dlock8/Selftest_Board/selftest_bd/connector.kicad_sch

## KiCad design selftest_bd/connector.kicad_sch (2025-02-06)

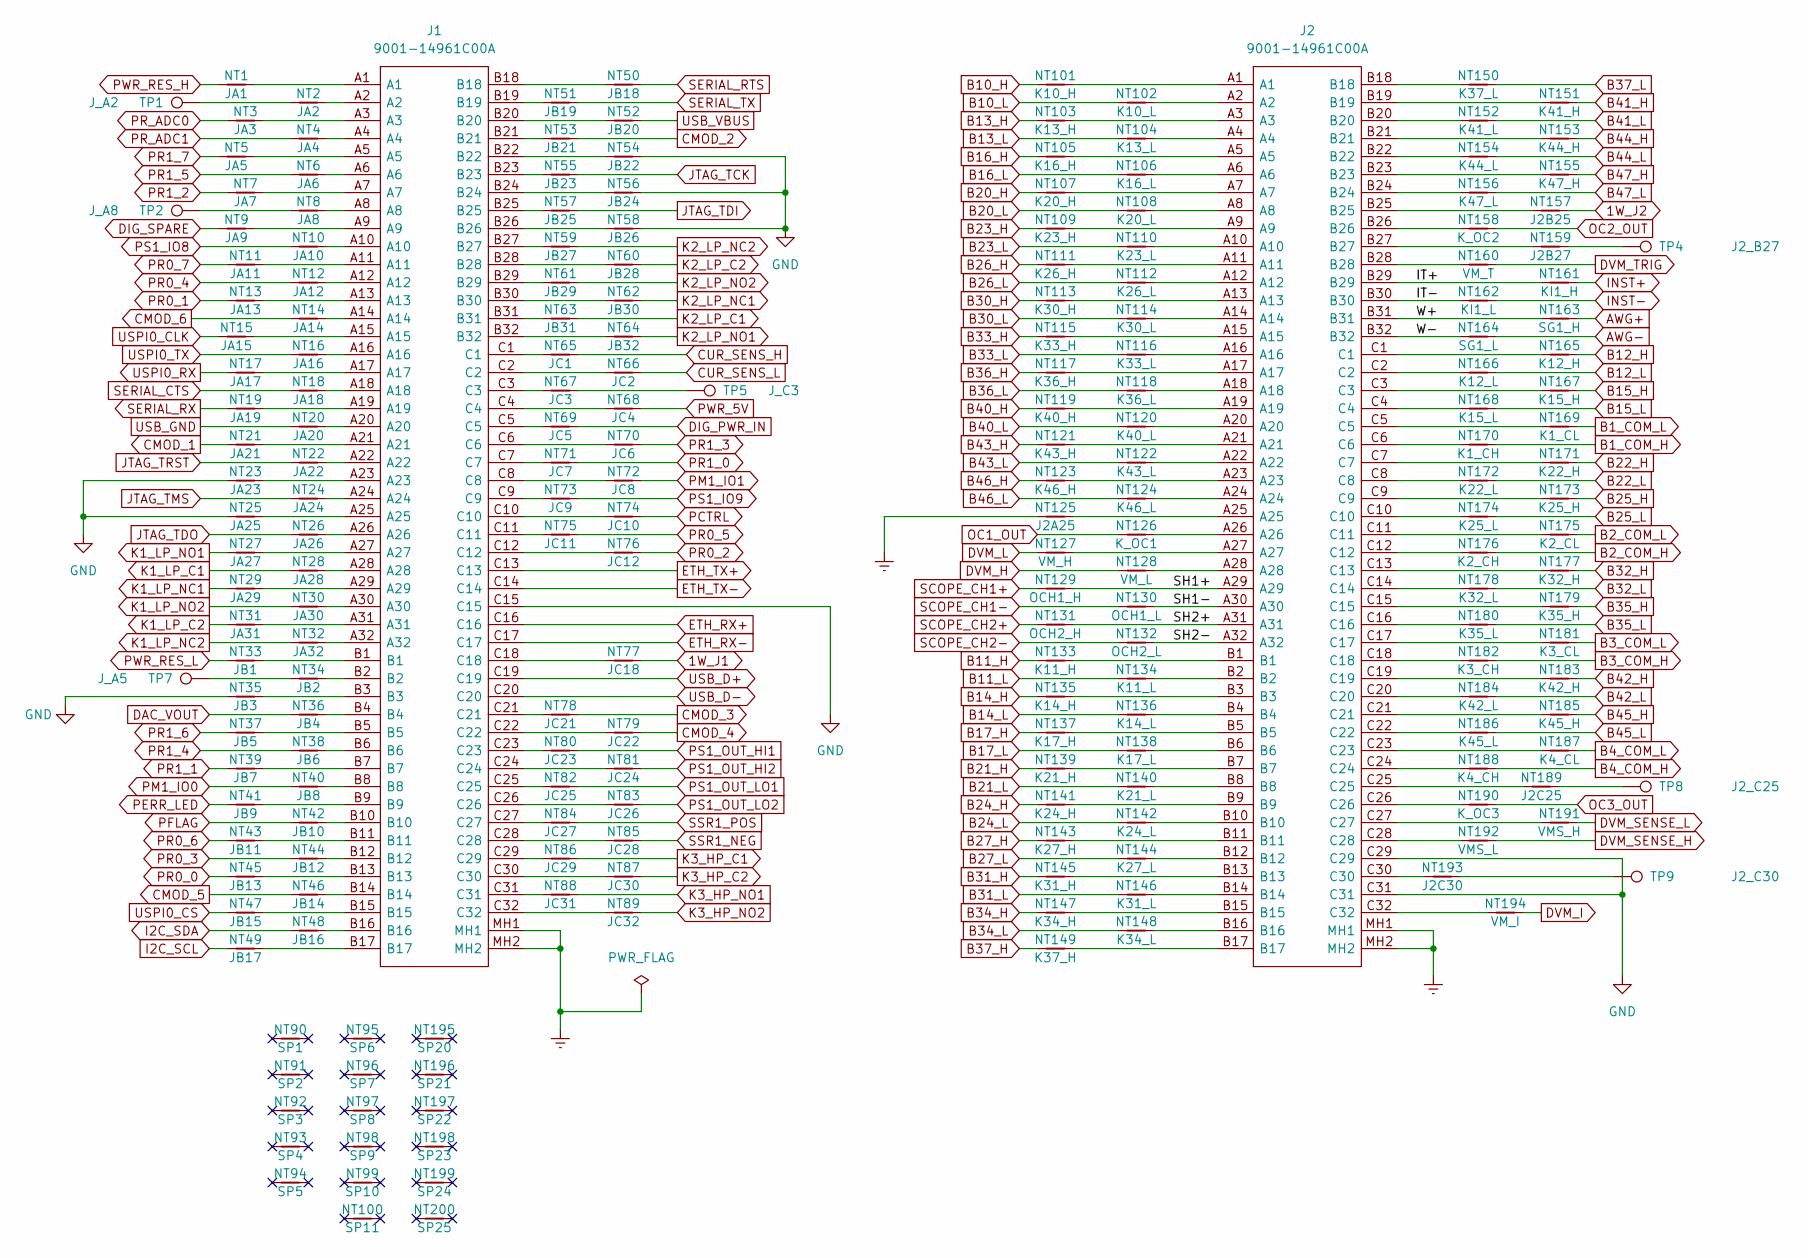
[picture p23: schematic connector.kicad_sch]

Parts:
J1, J2: 9001-14961C00A; 900114961C00A; Manufacturer_Part_Number 9001-14961C00A
NT1: JA1; NetTie-2_Front1.0mm
NT2: JA2; NetTie-2_Front1.0mm
NT3: JA3; NetTie-2_Front1.0mm
NT4: JA4; NetTie-2_Front1.0mm
NT5: JA5; NetTie-2_Front1.0mm
NT6: JA6; NetTie-2_Front1.0mm
NT7: JA7; NetTie-2_Front1.0mm
NT8: JA8; NetTie-2_Front1.0mm
NT9: JA9; NetTie-2_Front1.0mm
NT10: JA10; NetTie-2_Front1.0mm
NT11: JA11; NetTie-2_Front1.0mm
NT12: JA12; NetTie-2_Front1.0mm
NT13: JA13; NetTie-2_Front1.0mm
NT14: JA14; NetTie-2_Front1.0mm
NT15: JA15; NetTie-2_Front1.0mm
NT16: JA16; NetTie-2_Front1.0mm
NT17: JA17; NetTie-2_Front1.0mm
NT18: JA18; NetTie-2_Front1.0mm
NT19: JA19; NetTie-2_Front1.0mm
NT20: JA20; NetTie-2_Front1.0mm
NT21: JA21; NetTie-2_Front1.0mm
NT22: JA22; NetTie-2_Front1.0mm
NT23: JA23; NetTie-2_Front1.0mm
NT24: JA24; NetTie-2_Front1.0mm
NT25: JA25; NetTie-2_Front1.0mm
NT26: JA26; NetTie-2_Front1.0mm
NT27: JA27; NetTie-2_Front1.0mm
NT28: JA28; NetTie-2_Front1.0mm
NT29: JA29; NetTie-2_Front1.0mm
NT30: JA30; NetTie-2_Front1.0mm
NT31: JA31; NetTie-2_Front1.0mm
NT32: JA32; NetTie-2_Front1.0mm
NT33: JB1; NetTie-2_Front1.0mm
NT34: JB2; NetTie-2_Front1.0mm
NT35: JB3; NetTie-2_Front1.0mm
NT36: JB4; NetTie-2_Front1.0mm
NT37: JB5; NetTie-2_Front1.0mm
NT38: JB6; NetTie-2_Front1.0mm
NT39: JB7; NetTie-2_Front1.0mm
NT40: JB8; NetTie-2_Front1.0mm
NT41: JB9; NetTie-2_Front1.0mm
NT42: JB10; NetTie-2_Front1.0mm
NT43: JB11; NetTie-2_Front1.0mm
NT44: JB12; NetTie-2_Front1.0mm
NT45: JB13; NetTie-2_Front1.0mm
NT46: JB14; NetTie-2_Front1.0mm
NT47: JB15; NetTie-2_Front1.0mm
NT48: JB16; NetTie-2_Front1.0mm
NT49: JB17; NetTie-2_Front1.0mm
NT50: JB18; NetTie-2_Front1.0mm
NT51: JB19; NetTie-2_Front1.0mm
NT52: JB20; NetTie-2_Front1.0mm
NT53: JB21; NetTie-2_Front1.0mm
NT54: JB22; NetTie-2_Front1.0mm
NT55: JB23; NetTie-2_Front1.0mm
NT56: JB24; NetTie-2_Front1.0mm
NT57: JB25; NetTie-2_Front1.0mm
NT58: JB26; NetTie-2_Front1.0mm
NT59: JB27; NetTie-2_Front1.0mm
NT60: JB28; NetTie-2_Front1.0mm
NT61: JB29; NetTie-2_Front1.0mm
NT62: JB30; NetTie-2_Front1.0mm
NT63: JB31; NetTie-2_Front1.0mm
NT64: JB32; NetTie-2_Front1.0mm
NT65: JC1; NetTie-2_Front1.0mm
NT66: JC2; NetTie-2_Front1.0mm
NT67: JC3; NetTie-2_Front1.0mm
NT68: JC4; NetTie-2_Front1.0mm
NT69: JC5; NetTie-2_Front1.0mm
NT70: JC6; NetTie-2_Front1.0mm
NT71: JC7; NetTie-2_Front1.0mm
NT72: JC8; NetTie-2_Front1.0mm
NT73: JC9; NetTie-2_Front1.0mm
NT74: JC10; NetTie-2_Front1.0mm
NT75: JC11; NetTie-2_Front1.0mm
NT76: JC12; NetTie-2_Front1.0mm
NT77: JC18; NetTie-2_Front1.0mm
NT78: JC21; NetTie-2_Front1.0mm
NT79: JC22; NetTie-2_Front1.0mm
NT80: JC23; NetTie-2_Front1.0mm
NT81: JC24; NetTie-2_Front1.0mm
NT82: JC25; NetTie-2_Front1.0mm
NT83: JC26; NetTie-2_Front1.0mm
NT84: JC27; NetTie-2_Front1.0mm
NT85: JC28; NetTie-2_Front1.0mm
NT86: JC29; NetTie-2_Front1.0mm
NT87: JC30; NetTie-2_Front1.0mm
NT88: JC31; NetTie-2_Front1.0mm
NT89: JC32; NetTie-2_Front1.0mm
NT90: SP1; NetTie-2_Front1.0mm
NT91: SP2; NetTie-2_Front1.0mm
NT92: SP3; NetTie-2_Front1.0mm
NT93: SP4; NetTie-2_Front1.0mm
NT94: SP5; NetTie-2_Front1.0mm
NT95: SP6; NetTie-2_Front1.0mm
NT96: SP7; NetTie-2_Front1.0mm
NT97: SP8; NetTie-2_Front1.0mm
NT98: SP9; NetTie-2_Front1.0mm
NT99: SP10; NetTie-2_Front1.0mm
NT100: SP11; NetTie-2_Front1.0mm
NT101: K10_H; NetTie-2_Front1.0mm
NT102: K10_L; NetTie-2_Front1.0mm
NT103: K13_H; NetTie-2_Front1.0mm
NT104: K13_L; NetTie-2_Front1.0mm
NT105: K16_H; NetTie-2_Front1.0mm
NT106: K16_L; NetTie-2_Front1.0mm
NT107: K20_H; NetTie-2_Front1.0mm
NT108: K20_L; NetTie-2_Front1.0mm
NT109: K23_H; NetTie-2_Front1.0mm
NT110: K23_L; NetTie-2_Front1.0mm
NT111: K26_H; NetTie-2_Front1.0mm
NT112: K26_L; NetTie-2_Front1.0mm
NT113: K30_H; NetTie-2_Front1.0mm
NT114: K30_L; NetTie-2_Front1.0mm
NT115: K33_H; NetTie-2_Front1.0mm
NT116: K33_L; NetTie-2_Front1.0mm
NT117: K36_H; NetTie-2_Front1.0mm
NT118: K36_L; NetTie-2_Front1.0mm
NT119: K40_H; NetTie-2_Front1.0mm
NT120: K40_L; NetTie-2_Front1.0mm
NT121: K43_H; NetTie-2_Front1.0mm
NT122: K43_L; NetTie-2_Front1.0mm
NT123: K46_H; NetTie-2_Front1.0mm
NT124: K46_L; NetTie-2_Front1.0mm
NT125: J2A25; NetTie-2_Front1.0mm
NT126: K_OC1; NetTie-2_Front1.0mm
NT127: VM_H; NetTie-2_Front1.0mm
NT128: VM_L; NetTie-2_Front1.0mm
NT129: OCH1_H; NetTie-2_Front1.0mm
NT130: OCH1_L; NetTie-2_Front1.0mm
NT131: OCH2_H; NetTie-2_Front1.0mm
NT132: OCH2_L; NetTie-2_Front1.0mm
NT133: K11_H; NetTie-2_Front1.0mm
NT134: K11_L; NetTie-2_Front1.0mm
NT135: K14_H; NetTie-2_Front1.0mm
NT136: K14_L; NetTie-2_Front1.0mm
NT137: K17_H; NetTie-2_Front1.0mm
NT138: K17_L; NetTie-2_Front1.0mm
NT139: K21_H; NetTie-2_Front1.0mm
NT140: K21_L; NetTie-2_Front1.0mm
NT141: K24_H; NetTie-2_Front1.0mm
NT142: K24_L; NetTie-2_Front1.0mm
NT143: K27_H; NetTie-2_Front1.0mm
NT144: K27_L; NetTie-2_Front1.0mm
NT145: K31_H; NetTie-2_Front1.0mm
NT146: K31_L; NetTie-2_Front1.0mm
NT147: K34_H; NetTie-2_Front1.0mm
NT148: K34_L; NetTie-2_Front1.0mm
NT149: K37_H; NetTie-2_Front1.0mm
NT150: K37_L; NetTie-2_Front1.0mm
NT151: K41_H; NetTie-2_Front1.0mm
NT152: K41_L; NetTie-2_Front1.0mm
NT153: K44_H; NetTie-2_Front1.0mm
NT154: K44_L; NetTie-2_Front1.0mm
NT155: K47_H; NetTie-2_Front1.0mm
NT156: K47_L; NetTie-2_Front1.0mm
NT157: J2B25; NetTie-2_Front1.0mm
NT158: K_OC2; NetTie-2_Front1.0mm
NT159: J2B27; NetTie-2_Front1.0mm
NT160: VM_T; NetTie-2_Front1.0mm
NT161: KI1_H; NetTie-2_Front1.0mm
NT162: KI1_L; NetTie-2_Front1.0mm
NT163: SG1_H; NetTie-2_Front1.0mm
NT164: SG1_L; NetTie-2_Front1.0mm
NT165: K12_H; NetTie-2_Front1.0mm
NT166: K12_L; NetTie-2_Front1.0mm
NT167: K15_H; NetTie-2_Front1.0mm
NT168: K15_L; NetTie-2_Front1.0mm
NT169: K1_CL; NetTie-2_Front1.0mm
NT170: K1_CH; NetTie-2_Front1.0mm
NT171: K22_H; NetTie-2_Front1.0mm
NT172: K22_L; NetTie-2_Front1.0mm
NT173: K25_H; NetTie-2_Front1.0mm
NT174: K25_L; NetTie-2_Front1.0mm
NT175: K2_CL; NetTie-2_Front1.0mm
NT176: K2_CH; NetTie-2_Front1.0mm
NT177: K32_H; NetTie-2_Front1.0mm
NT178: K32_L; NetTie-2_Front1.0mm
NT179: K35_H; NetTie-2_Front1.0mm
NT180: K35_L; NetTie-2_Front1.0mm
NT181: K3_CL; NetTie-2_Front1.0mm
NT182: K3_CH; NetTie-2_Front1.0mm
NT183: K42_H; NetTie-2_Front1.0mm
NT184: K42_L; NetTie-2_Front1.0mm
NT185: K45_H; NetTie-2_Front1.0mm
NT186: K45_L; NetTie-2_Front1.0mm
NT187: K4_CL; NetTie-2_Front1.0mm
NT188: K4_CH; NetTie-2_Front1.0mm
NT189: J2C25; NetTie-2_Front1.0mm
NT190: K_OC3; NetTie-2_Front1.0mm
NT191: VMS_H; NetTie-2_Front1.0mm
NT192: VMS_L; NetTie-2_Front1.0mm
NT193: J2C30; NetTie-2_Front1.0mm
NT194: VM_I; NetTie-2_Front1.0mm
NT195: SP20; NetTie-2_Front1.0mm
NT196: SP21; NetTie-2_Front1.0mm
NT197: SP22; NetTie-2_Front1.0mm
NT198: SP23; NetTie-2_Front1.0mm
NT199: SP24; NetTie-2_Front1.0mm
NT200: SP25; NetTie-2_Front1.0mm
TP1: J_A2; TestPoint_THTPad_D1.5mm_Drill0.7mm
TP2: J_A8; TestPoint_THTPad_D1.5mm_Drill0.7mm
TP4: J2_B27; TestPoint_THTPad_D1.5mm_Drill0.7mm
TP5: J_C3; TestPoint_THTPad_D1.5mm_Drill0.7mm
TP7: J_A5; TestPoint_THTPad_D1.5mm_Drill0.7mm
TP8: J2_C25; TestPoint_THTPad_D1.5mm_Drill0.7mm
TP9: J2_C30; TestPoint_THTPad_D1.5mm_Drill0.7mm

Connections:
1W_J1: NT77.1
1W_J2: NT157.2
AWG+: NT163.2
AWG-: NT164.2
B1_COM_H: NT170.1
B1_COM_L: NT169.1
B2_COM_H: NT176.1
B2_COM_L: NT175.1
B3_COM_H: NT182.2
B3_COM_L: NT181.2
B4_COM_H: NT188.1
B4_COM_L: NT187.1
B10_H: NT101.2
B10_L: NT102.2
B11_H: NT133.2
B11_L: NT134.2
B12_H: NT165.2
B12_L: NT166.2
B13_H: NT103.2
B13_L: NT104.2
B14_H: NT135.2
B14_L: NT136.2
B15_H: NT167.2
B15_L: NT168.2
B16_H: NT105.2
B16_L: NT106.2
B17_H: NT137.2
B17_L: NT138.2
B20_H: NT107.2
B20_L: NT108.2
B21_H: NT139.2
B21_L: NT140.2
B22_H: NT171.2
B22_L: NT172.2
B23_H: NT109.2
B23_L: NT110.2
B24_H: NT141.2
B24_L: NT142.2
B25_H: NT173.2
B25_L: NT174.2
B26_H: NT111.2
B26_L: NT112.2
B27_H: NT143.2
B27_L: NT144.2
B30_H: NT113.2
B30_L: NT114.2
B31_H: NT145.2
B31_L: NT146.2
B32_H: NT177.2
B32_L: NT178.2
B33_H: NT115.2
B33_L: NT116.2
B34_H: NT147.2
B34_L: NT148.2
B35_H: NT179.2
B35_L: NT180.2
B36_H: NT117.2
B36_L: NT118.2
B37_H: NT149.2
B37_L: NT150.2
B40_H: NT119.2
B40_L: NT120.2
B41_H: NT151.2
B41_L: NT152.2
B42_H: NT183.1
B42_L: NT184.2
B43_H: NT121.2
B43_L: NT122.2
B44_H: NT153.2
B44_L: NT154.2
B45_H: NT185.2
B45_L: NT186.2
B46_H: NT123.2
B46_L: NT124.2
B47_H: NT155.2
B47_L: NT156.2
CMOD_1: NT21.1
CMOD_2: NT53.1
CMOD_3: NT78.1
CMOD_4: NT79.1
CMOD_5: NT46.1
CMOD_6: NT14.1
CUR_SENS_H: NT65.1
CUR_SENS_L: NT66.1
DAC_VOUT: NT36.1
DIG_PWR_IN: NT69.1
DIG_SPARE: NT9.1
DVM_H: NT128.2
DVM_I: NT194.2
DVM_L: NT127.2
DVM_SENSE_H: NT192.2
DVM_SENSE_L: NT191.2
DVM_TRIG: NT160.2
ETH_RX+: J1.C16
ETH_RX-: J1.C17
ETH_TX+: J1.C13
ETH_TX-: J1.C14
Earth: J1.MH1, J1.MH2, J2.MH1, J2.MH2, NT125.2
GND: J1.C15, J2.C29, J2.C31, NT23.1, NT25.1, NT35.1, NT54.1, NT56.1, NT58.1
I2C_SCL: NT49.1
I2C_SDA: NT48.1
INST+: NT161.1
INST-: NT162.1
IT+: J2.B29, NT161.2
IT-: J2.B30, NT162.2
JTAG_TCK: NT55.1
JTAG_TDI: NT57.1
JTAG_TDO: NT26.1
JTAG_TMS: NT24.1
JTAG_TRST: NT22.1
K1_LP_C1: NT28.1
K1_LP_C2: NT31.1
K1_LP_NC1: NT29.1
K1_LP_NC2: NT32.1
K1_LP_NO1: NT27.1
K1_LP_NO2: NT30.1
K2_LP_C1: NT63.1
K2_LP_C2: NT60.1
K2_LP_NC1: NT62.1
K2_LP_NC2: NT59.1
K2_LP_NO1: NT64.1
K2_LP_NO2: NT61.1
K3_HP_C1: NT86.1
K3_HP_C2: NT87.1
K3_HP_NO1: NT88.1
K3_HP_NO2: NT89.1
unnamed: J1.A1, NT1.2
unnamed: J1.A2, NT2.2
unnamed: J1.A3, NT3.2
unnamed: J1.A4, NT4.2
unnamed: J1.A5, NT5.2
unnamed: J1.A6, NT6.2
unnamed: J1.A7, NT7.2
unnamed: J1.A8, NT8.2
unnamed: J1.A9, NT9.2
unnamed: J1.A10, NT10.2
unnamed: J1.A11, NT11.2
unnamed: J1.A12, NT12.2
unnamed: J1.A13, NT13.2
unnamed: J1.A14, NT14.2
unnamed: J1.A15, NT15.2
unnamed: J1.A16, NT16.2
unnamed: J1.A17, NT17.2
unnamed: J1.A18, NT18.2
unnamed: J1.A19, NT19.2
unnamed: J1.A20, NT20.2
unnamed: J1.A21, NT21.2
unnamed: J1.A22, NT22.2
unnamed: J1.A23, NT23.2
unnamed: J1.A24, NT24.2
unnamed: J1.A25, NT25.2
unnamed: J1.A26, NT26.2
unnamed: J1.A27, NT27.2
unnamed: J1.A28, NT28.2
unnamed: J1.A29, NT29.2
unnamed: J1.A30, NT30.2
unnamed: J1.A31, NT31.2
unnamed: J1.A32, NT32.2
unnamed: J1.B1, NT33.2
unnamed: J1.B2, NT34.2
unnamed: J1.B3, NT35.2
unnamed: J1.B4, NT36.2
unnamed: J1.B5, NT37.2
unnamed: J1.B6, NT38.2
unnamed: J1.B7, NT39.2
unnamed: J1.B8, NT40.2
unnamed: J1.B9, NT41.2
unnamed: J1.B10, NT42.2
unnamed: J1.B11, NT43.2
unnamed: J1.B12, NT44.2
unnamed: J1.B13, NT45.2
unnamed: J1.B14, NT46.2
unnamed: J1.B15, NT47.2
unnamed: J1.B16, NT48.2
unnamed: J1.B17, NT49.2
unnamed: J1.B18, NT50.2
unnamed: J1.B19, NT51.2
unnamed: J1.B20, NT52.2
unnamed: J1.B21, NT53.2
unnamed: J1.B22, NT54.2
unnamed: J1.B23, NT55.2
unnamed: J1.B24, NT56.2
unnamed: J1.B25, NT57.2
unnamed: J1.B26, NT58.2
unnamed: J1.B27, NT59.2
unnamed: J1.B28, NT60.2
unnamed: J1.B29, NT61.2
unnamed: J1.B30, NT62.2
unnamed: J1.B31, NT63.2
unnamed: J1.B32, NT64.2
unnamed: J1.C1, NT65.2
unnamed: J1.C2, NT66.2
unnamed: J1.C3, NT67.2
unnamed: J1.C4, NT68.2
unnamed: J1.C5, NT69.2
unnamed: J1.C6, NT70.2
unnamed: J1.C7, NT71.2
unnamed: J1.C8, NT72.2
unnamed: J1.C9, NT73.2
unnamed: J1.C10, NT74.2
unnamed: J1.C11, NT75.2
unnamed: J1.C12, NT76.2
unnamed: J1.C18, NT77.2
unnamed: J1.C21, NT78.2
unnamed: J1.C22, NT79.2
unnamed: J1.C23, NT80.2
unnamed: J1.C24, NT81.2
unnamed: J1.C25, NT82.2
unnamed: J1.C26, NT83.2
unnamed: J1.C27, NT84.2
unnamed: J1.C28, NT85.2
unnamed: J1.C29, NT86.2
unnamed: J1.C30, NT87.2
unnamed: J1.C31, NT88.2
unnamed: J1.C32, NT89.2
unnamed: J2.A1, NT101.1
unnamed: J2.A2, NT102.1
unnamed: J2.A3, NT103.1
unnamed: J2.A4, NT104.1
unnamed: J2.A5, NT105.1
unnamed: J2.A6, NT106.1
unnamed: J2.A7, NT107.1
unnamed: J2.A8, NT108.1
unnamed: J2.A9, NT109.1
unnamed: J2.A10, NT110.1
unnamed: J2.A11, NT111.1
unnamed: J2.A12, NT112.1
unnamed: J2.A13, NT113.1
unnamed: J2.A14, NT114.1
unnamed: J2.A15, NT115.1
unnamed: J2.A16, NT116.1
unnamed: J2.A17, NT117.1
unnamed: J2.A18, NT118.1
unnamed: J2.A19, NT119.1
unnamed: J2.A20, NT120.1
unnamed: J2.A21, NT121.1
unnamed: J2.A22, NT122.1
unnamed: J2.A23, NT123.1
unnamed: J2.A24, NT124.1
unnamed: J2.A25, NT125.1
unnamed: J2.A26, NT126.2
unnamed: J2.A27, NT127.1
unnamed: J2.A28, NT128.1
unnamed: J2.B1, NT133.1
unnamed: J2.B2, NT134.1
unnamed: J2.B3, NT135.1
unnamed: J2.B4, NT136.1
unnamed: J2.B5, NT137.1
unnamed: J2.B6, NT138.1
unnamed: J2.B7, NT139.1
unnamed: J2.B8, NT140.1
unnamed: J2.B9, NT141.1
unnamed: J2.B10, NT142.1
unnamed: J2.B11, NT143.1
unnamed: J2.B12, NT144.1
unnamed: J2.B13, NT145.1
unnamed: J2.B14, NT146.1
unnamed: J2.B15, NT147.1
unnamed: J2.B16, NT148.1
unnamed: J2.B17, NT149.1
unnamed: J2.B18, NT150.1
unnamed: J2.B19, NT151.1
unnamed: J2.B20, NT152.1
unnamed: J2.B21, NT153.1
unnamed: J2.B22, NT154.1
unnamed: J2.B23, NT155.1
unnamed: J2.B24, NT156.1
unnamed: J2.B25, NT157.1
unnamed: J2.B26, NT158.2
unnamed: J2.B27, NT159.1
unnamed: J2.B28, NT160.1
unnamed: J2.C1, NT165.1
unnamed: J2.C2, NT166.1
unnamed: J2.C3, NT167.1
unnamed: J2.C4, NT168.1
unnamed: J2.C5, NT169.2
unnamed: J2.C6, NT170.2
unnamed: J2.C7, NT171.1
unnamed: J2.C8, NT172.1
unnamed: J2.C9, NT173.1
unnamed: J2.C10, NT174.1
unnamed: J2.C11, NT175.2
unnamed: J2.C12, NT176.2
unnamed: J2.C13, NT177.1
unnamed: J2.C14, NT178.1
unnamed: J2.C15, NT179.1
unnamed: J2.C16, NT180.1
unnamed: J2.C17, NT181.1
unnamed: J2.C18, NT182.1
unnamed: J2.C19, NT183.2
unnamed: J2.C20, NT184.1
unnamed: J2.C21, NT185.1
unnamed: J2.C22, NT186.1
unnamed: J2.C23, NT187.2
unnamed: J2.C24, NT188.2
unnamed: J2.C25, NT189.2
unnamed: J2.C26, NT190.2
unnamed: J2.C27, NT191.1
unnamed: J2.C28, NT192.1
unnamed: J2.C30, NT193.1
unnamed: J2.C32, NT194.1
unnamed: NT2.1, TP1.1
unnamed: NT8.1, TP2.1
unnamed: NT34.1, TP7.1
unnamed: NT67.1, TP5.1
unnamed: NT159.2, TP4.1
unnamed: NT189.1, TP8.1
unnamed: NT193.2, TP9.1
OC1_OUT: NT126.1
OC2_OUT: NT158.1
OC3_OUT: NT190.1
PCTRL: NT74.1
PERR_LED: NT41.1
PFLAG: NT42.1
PM1_IO0: NT40.1
PM1_IO1: NT72.1
PR0_0: NT45.1
PR0_1: NT13.1
PR0_2: NT76.1
PR0_3: NT44.1
PR0_4: NT12.1
PR0_5: NT75.1
PR0_6: NT43.1
PR0_7: NT11.1
PR1_0: NT71.1
PR1_1: NT39.1
PR1_2: NT7.1
PR1_3: NT70.1
PR1_4: NT38.1
PR1_5: NT6.1
PR1_6: NT37.1
PR1_7: NT5.1
PR_ADC0: NT3.1
PR_ADC1: NT4.1
PS1_IO8: NT10.1
PS1_IO9: NT73.1
PS1_OUT_HI1: NT80.1
PS1_OUT_HI2: NT81.1
PS1_OUT_LO1: NT82.1
PS1_OUT_LO2: NT83.1
PWR_5V: NT68.1
PWR_RES_H: NT1.1
PWR_RES_L: NT33.1
SCOPE_CH1+: NT129.2
SCOPE_CH1-: NT130.2
SCOPE_CH2+: NT131.1
SCOPE_CH2-: NT132.1
SERIAL_CTS: NT18.1
SERIAL_RTS: NT50.1
SERIAL_RX: NT19.1
SERIAL_TX: NT51.1
SH1+: J2.A29, NT129.1
SH1-: J2.A30, NT130.1
SH2+: J2.A31, NT131.2
SH2-: J2.A32, NT132.2
SSR1_NEG: NT85.1
SSR1_POS: NT84.1
USB_D+: J1.C19
USB_D-: J1.C20
USB_GND: NT20.1
USB_VBUS: NT52.1
USPI0_CLK: NT15.1
USPI0_CS: NT47.1
USPI0_RX: NT17.1
USPI0_TX: NT16.1
W+: J2.B31, NT163.1
W-: J2.B32, NT164.1
