dlock8/Selftest_Board/selftest_bd/controller.kicad_sch

## KiCad design selftest_bd/controller.kicad_sch (2024-11-22)

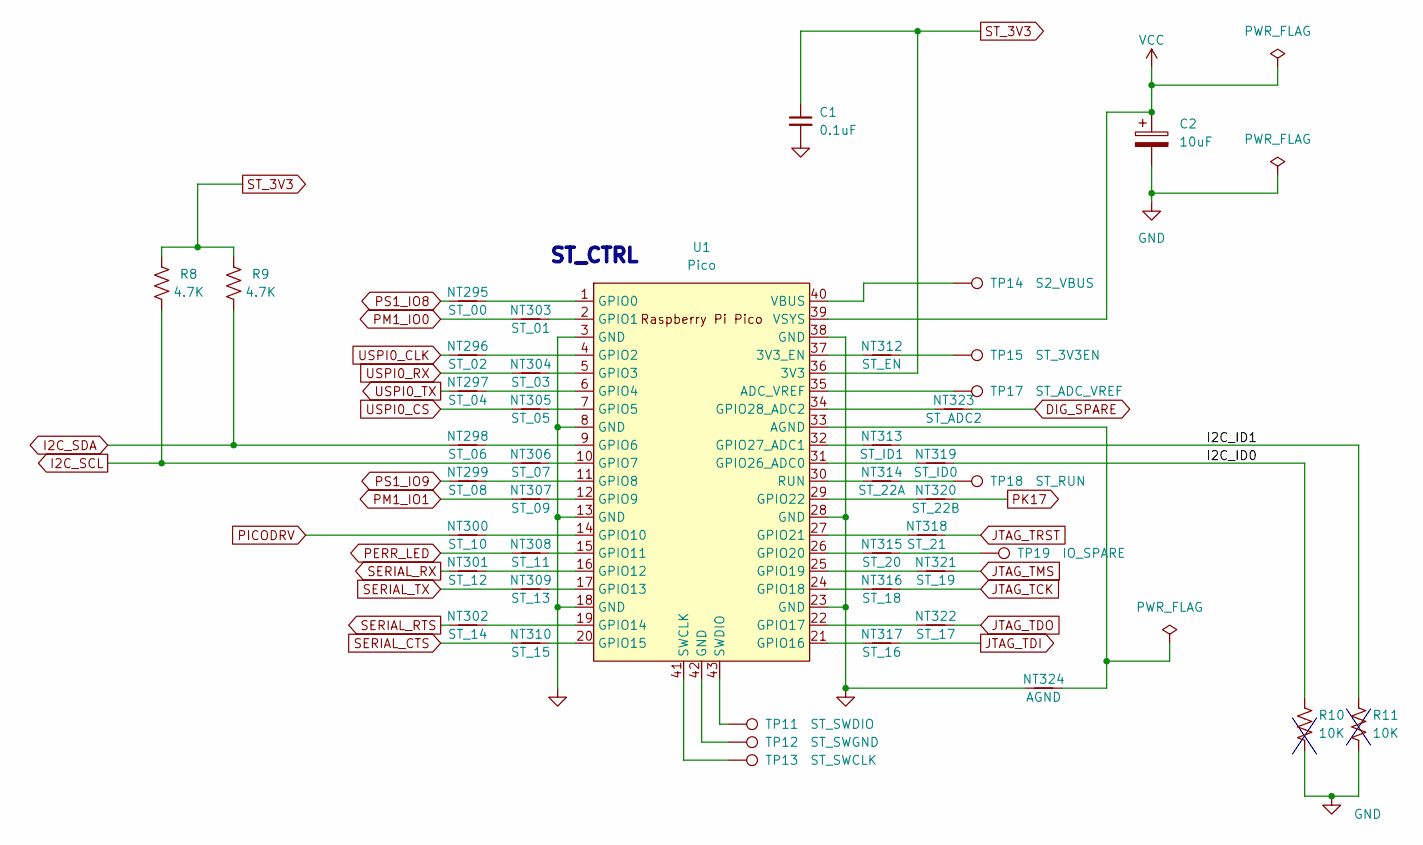
[picture p24: schematic controller.kicad_sch]

Parts:
C1: 0.1uF; C_Disc_D6.0mm_W2.5mm_P5.00mm
C2: 10uF; CP_Radial_Tantal_D4.5mm_P2.50mm
NT295: ST_00; NetTie-2_Front1.0mm
NT296: ST_02; NetTie-2_Front1.0mm
NT297: ST_04; NetTie-2_Front1.0mm
NT298: ST_06; NetTie-2_Front1.0mm
NT299: ST_08; NetTie-2_Front1.0mm
NT300: ST_10; NetTie-2_Front1.0mm
NT301: ST_12; NetTie-2_Front1.0mm
NT302: ST_14; NetTie-2_Front1.0mm
NT303: ST_01; NetTie-2_Front1.0mm
NT304: ST_03; NetTie-2_Front1.0mm
NT305: ST_05; NetTie-2_Front1.0mm
NT306: ST_07; NetTie-2_Front1.0mm
NT307: ST_09; NetTie-2_Front1.0mm
NT308: ST_11; NetTie-2_Front1.0mm
NT309: ST_13; NetTie-2_Front1.0mm
NT310: ST_15; NetTie-2_Front1.0mm
NT312: ST_EN; NetTie-2_Front1.0mm
NT313: ST_ID1; NetTie-2_Front1.0mm
NT314: ST_22A; NetTie-2_Front1.0mm
NT315: ST_20; NetTie-2_Front1.0mm
NT316: ST_18; NetTie-2_Front1.0mm
NT317: ST_16; NetTie-2_Front1.0mm
NT318: ST_21; NetTie-2_Front1.0mm
NT319: ST_ID0; NetTie-2_Front1.0mm
NT320: ST_22B; NetTie-2_Front1.0mm
NT321: ST_19; NetTie-2_Front1.0mm
NT322: ST_17; NetTie-2_Front1.0mm
NT323: ST_ADC2; NetTie-2_Front1.0mm
NT324: AGND; NetTie-2_Front1.0mm
R8, R9: 4.7K; R_Axial_DIN0207_L6.3mm_D2.5mm_P10.16mm_Horizontal
R10, R11: 10K; R_Axial_DIN0207_L6.3mm_D2.5mm_P10.16mm_Horizontal
TP11: ST_SWDIO; TestPoint_THTPad_D1.5mm_Drill0.7mm
TP12: ST_SWGND; TestPoint_THTPad_D1.5mm_Drill0.7mm
TP13: ST_SWCLK; TestPoint_THTPad_D1.5mm_Drill0.7mm
TP14: S2_VBUS; TestPoint_THTPad_D1.5mm_Drill0.7mm
TP15: ST_3V3EN; TestPoint_THTPad_D1.5mm_Drill0.7mm
TP17: ST_ADC_VREF; TestPoint_THTPad_D1.5mm_Drill0.7mm
TP18: ST_RUN; TestPoint_THTPad_D1.5mm_Drill0.7mm
TP19: IO_SPARE; TestPoint_THTPad_D1.5mm_Drill0.7mm
U1: Pico; RPi_Pico_SMD_TH

Connections:
DIG_SPARE: NT323.1
GND: C1.2, C2.2, NT324.2, R10.1, R11.1, U1.3 (GND), U1.8 (GND), U1.13 (GND), U1.18 (GND), U1.23 (GND), U1.28 (GND), U1.38 (GND)
I2C_ID0: NT319.1, R10.2
I2C_ID1: NT313.1, R11.2
I2C_SCL: NT306.1, R8.1
I2C_SDA: NT298.1, R9.1
JTAG_TCK: NT316.1
JTAG_TDI: NT317.1
JTAG_TDO: NT322.1
JTAG_TMS: NT321.1
JTAG_TRST: NT318.1
unnamed: NT295.2, U1.1 (GPIO0)
unnamed: NT296.2, U1.4 (GPIO2)
unnamed: NT297.2, U1.6 (GPIO4)
unnamed: NT298.2, U1.9 (GPIO6)
unnamed: NT299.2, U1.11 (GPIO8)
unnamed: NT300.2, U1.14 (GPIO10)
unnamed: NT301.2, U1.16 (GPIO12)
unnamed: NT302.2, U1.19 (GPIO14)
unnamed: NT303.2, U1.2 (GPIO1)
unnamed: NT304.2, U1.5 (GPIO3)
unnamed: NT305.2, U1.7 (GPIO5)
unnamed: NT306.2, U1.10 (GPIO7)
unnamed: NT307.2, U1.12 (GPIO9)
unnamed: NT308.2, U1.15 (GPIO11)
unnamed: NT309.2, U1.17 (GPIO13)
unnamed: NT310.2, U1.20 (GPIO15)
unnamed: NT312.1, U1.37 (3V3_EN)
unnamed: NT312.2, TP15.1
unnamed: NT313.2, U1.32 (GPIO27_ADC1)
unnamed: NT314.1, U1.30 (RUN)
unnamed: NT314.2, TP18.1
unnamed: NT315.1, TP19.1
unnamed: NT315.2, U1.26 (GPIO20)
unnamed: NT316.2, U1.24 (GPIO18)
unnamed: NT317.2, U1.21 (GPIO16)
unnamed: NT318.2, U1.27 (GPIO21)
unnamed: NT319.2, U1.31 (GPIO26_ADC0)
unnamed: NT320.1, U1.29 (GPIO22)
unnamed: NT321.2, U1.25 (GPIO19)
unnamed: NT322.2, U1.22 (GPIO17)
unnamed: NT323.2, U1.34 (GPIO28_ADC2)
unnamed: NT324.1, U1.33 (AGND)
unnamed: TP11.1, U1.43 (SWDIO)
unnamed: TP12.1, U1.42 (GND)
unnamed: TP13.1, U1.41 (SWCLK)
unnamed: TP14.1, U1.40 (VBUS)
unnamed: TP17.1, U1.35 (ADC_VREF)
PERR_LED: NT308.1
PICODRV: NT300.1
PK17: NT320.2
PM1_IO0: NT303.1
PM1_IO1: NT307.1
PS1_IO8: NT295.1
PS1_IO9: NT299.1
SERIAL_CTS: NT310.1
SERIAL_RTS: NT302.1
SERIAL_RX: NT301.1
SERIAL_TX: NT309.1
ST_3V3: C1.1, R8.2, R9.2, U1.36 (3V3)
USPI0_CLK: NT296.1
USPI0_CS: NT305.1
USPI0_RX: NT304.1
USPI0_TX: NT297.1
VCC: C2.1, U1.39 (VSYS)

Notes on the sheet:
ST_CTRL
