dlock8/Selftest_Board/selftest_bd/relay_driver.kicad_sch

## KiCad design selftest_bd/relay_driver.kicad_sch (2024-11-22)

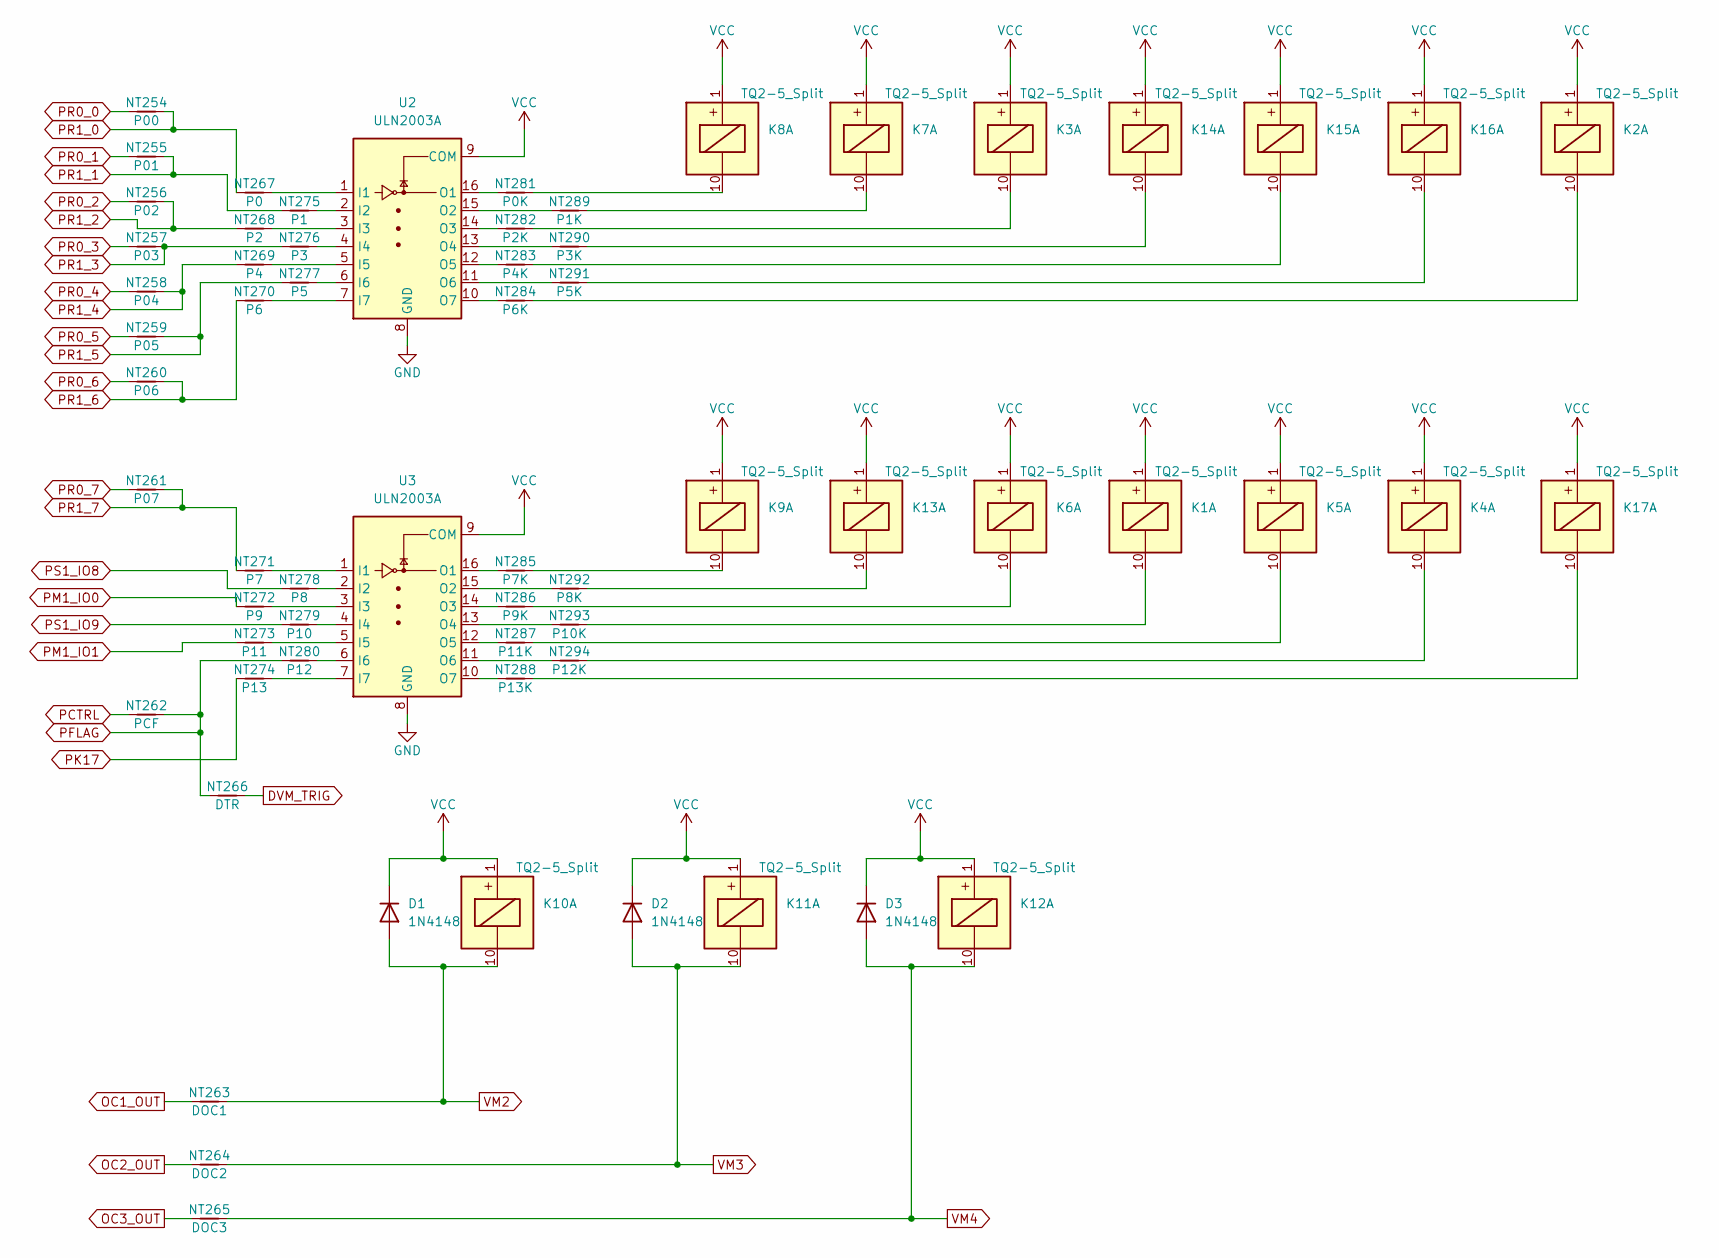
[picture p25: schematic relay_driver.kicad_sch]

Parts:
D1, D2, D3: 1N4148; D_DO-35_SOD27_P7.62mm_Horizontal
K1, K2, K3, K4, K5, K6, K7, K8, K9, K10, K11, K12, K13, K14, K15, K16, K17: TQ2-5_Split; Relay_DPDT_FRT5
NT254: P00; NetTie-2_Front1.0mm
NT255: P01; NetTie-2_Front1.0mm
NT256: P02; NetTie-2_Front1.0mm
NT257: P03; NetTie-2_Front1.0mm
NT258: P04; NetTie-2_Front1.0mm
NT259: P05; NetTie-2_Front1.0mm
NT260: P06; NetTie-2_Front1.0mm
NT261: P07; NetTie-2_Front1.0mm
NT262: PCF; NetTie-2_Front1.0mm
NT263: DOC1; NetTie-2_Front1.0mm
NT264: DOC2; NetTie-2_Front1.0mm
NT265: DOC3; NetTie-2_Front1.0mm
NT266: DTR; NetTie-2_Front1.0mm
NT267: P0; NetTie-2_Front1.0mm
NT268: P2; NetTie-2_Front1.0mm
NT269: P4; NetTie-2_Front1.0mm
NT270: P6; NetTie-2_Front1.0mm
NT271: P7; NetTie-2_Front1.0mm
NT272: P9; NetTie-2_Front1.0mm
NT273: P11; NetTie-2_Front1.0mm
NT274: P13; NetTie-2_Front1.0mm
NT275: P1; NetTie-2_Front1.0mm
NT276: P3; NetTie-2_Front1.0mm
NT277: P5; NetTie-2_Front1.0mm
NT278: P8; NetTie-2_Front1.0mm
NT279: P10; NetTie-2_Front1.0mm
NT280: P12; NetTie-2_Front1.0mm
NT281: P0K; NetTie-2_Front1.0mm
NT282: P2K; NetTie-2_Front1.0mm
NT283: P4K; NetTie-2_Front1.0mm
NT284: P6K; NetTie-2_Front1.0mm
NT285: P7K; NetTie-2_Front1.0mm
NT286: P9K; NetTie-2_Front1.0mm
NT287: P11K; NetTie-2_Front1.0mm
NT288: P13K; NetTie-2_Front1.0mm
NT289: P1K; NetTie-2_Front1.0mm
NT290: P3K; NetTie-2_Front1.0mm
NT291: P5K; NetTie-2_Front1.0mm
NT292: P8K; NetTie-2_Front1.0mm
NT293: P10K; NetTie-2_Front1.0mm
NT294: P12K; NetTie-2_Front1.0mm
U2, U3: ULN2003A; DIP-16_W7.62mm_LongPads

Connections:
DVM_TRIG: NT266.2
GND: U2.8 (GND), U3.8 (GND)
unnamed: K1.10, NT293.2
unnamed: K2.10, NT284.2
unnamed: K3.10, NT282.2
unnamed: K4.10, NT294.2
unnamed: K5.10, NT287.2
unnamed: K6.10, NT286.2
unnamed: K7.10, NT289.2
unnamed: K8.10, NT281.2
unnamed: K9.10, NT285.2
unnamed: K13.10, NT292.2
unnamed: K14.10, NT290.2
unnamed: K15.10, NT283.2
unnamed: K16.10, NT291.2
unnamed: K17.10, NT288.2
unnamed: NT267.2, U2.1 (I1)
unnamed: NT268.2, U2.3 (I3)
unnamed: NT269.2, U2.5 (I5)
unnamed: NT270.2, U2.7 (I7)
unnamed: NT271.2, U3.1 (I1)
unnamed: NT272.2, U3.3 (I3)
unnamed: NT273.2, U3.5 (I5)
unnamed: NT274.2, U3.7 (I7)
unnamed: NT275.2, U2.2 (I2)
unnamed: NT276.2, U2.4 (I4)
unnamed: NT277.2, U2.6 (I6)
unnamed: NT278.2, U3.2 (I2)
unnamed: NT279.2, U3.4 (I4)
unnamed: NT280.2, U3.6 (I6)
unnamed: NT281.1, U2.16 (O1)
unnamed: NT282.1, U2.14 (O3)
unnamed: NT283.1, U2.12 (O5)
unnamed: NT284.1, U2.10 (O7)
unnamed: NT285.1, U3.16 (O1)
unnamed: NT286.1, U3.14 (O3)
unnamed: NT287.1, U3.12 (O5)
unnamed: NT288.1, U3.10 (O7)
unnamed: NT289.1, U2.15 (O2)
unnamed: NT290.1, U2.13 (O4)
unnamed: NT291.1, U2.11 (O6)
unnamed: NT292.1, U3.15 (O2)
unnamed: NT293.1, U3.13 (O4)
unnamed: NT294.1, U3.11 (O6)
OC1_OUT: NT263.2
OC2_OUT: NT264.2
OC3_OUT: NT265.2
PCTRL: NT262.1
PFLAG: NT262.2, NT266.1, NT280.1
PK17: NT274.1
PM1_IO0: NT272.1
PM1_IO1: NT273.1
PR0_0: NT254.1
PR0_1: NT255.1
PR0_2: NT256.1
PR0_3: NT257.1
PR0_4: NT258.1
PR0_5: NT259.1
PR0_6: NT260.1
PR0_7: NT261.1
PR1_0: NT254.2, NT267.1
PR1_1: NT255.2, NT275.1
PR1_2: NT256.2, NT268.1
PR1_3: NT257.2, NT276.1
PR1_4: NT258.2, NT269.1
PR1_5: NT259.2, NT277.1
PR1_6: NT260.2, NT270.1
PR1_7: NT261.2, NT271.1
PS1_IO8: NT278.1
PS1_IO9: NT279.1
VCC: D1.1 (K), D2.1 (K), D3.1 (K), K1.1, K2.1, K3.1, K4.1, K5.1, K6.1, K7.1, K8.1, K9.1, K10.1, K11.1, K12.1, K13.1, K14.1, K15.1, K16.1, K17.1, U2.9 (COM), U3.9 (COM)
VM2: D1.2 (A), K10.10, NT263.1
VM3: D2.2 (A), K11.10, NT264.1
VM4: D3.2 (A), K12.10, NT265.1
