dlock8/Selftest_Board/selftest_bd/relay_test.kicad_sch

## KiCad design selftest_bd/relay_test.kicad_sch (2025-02-06)

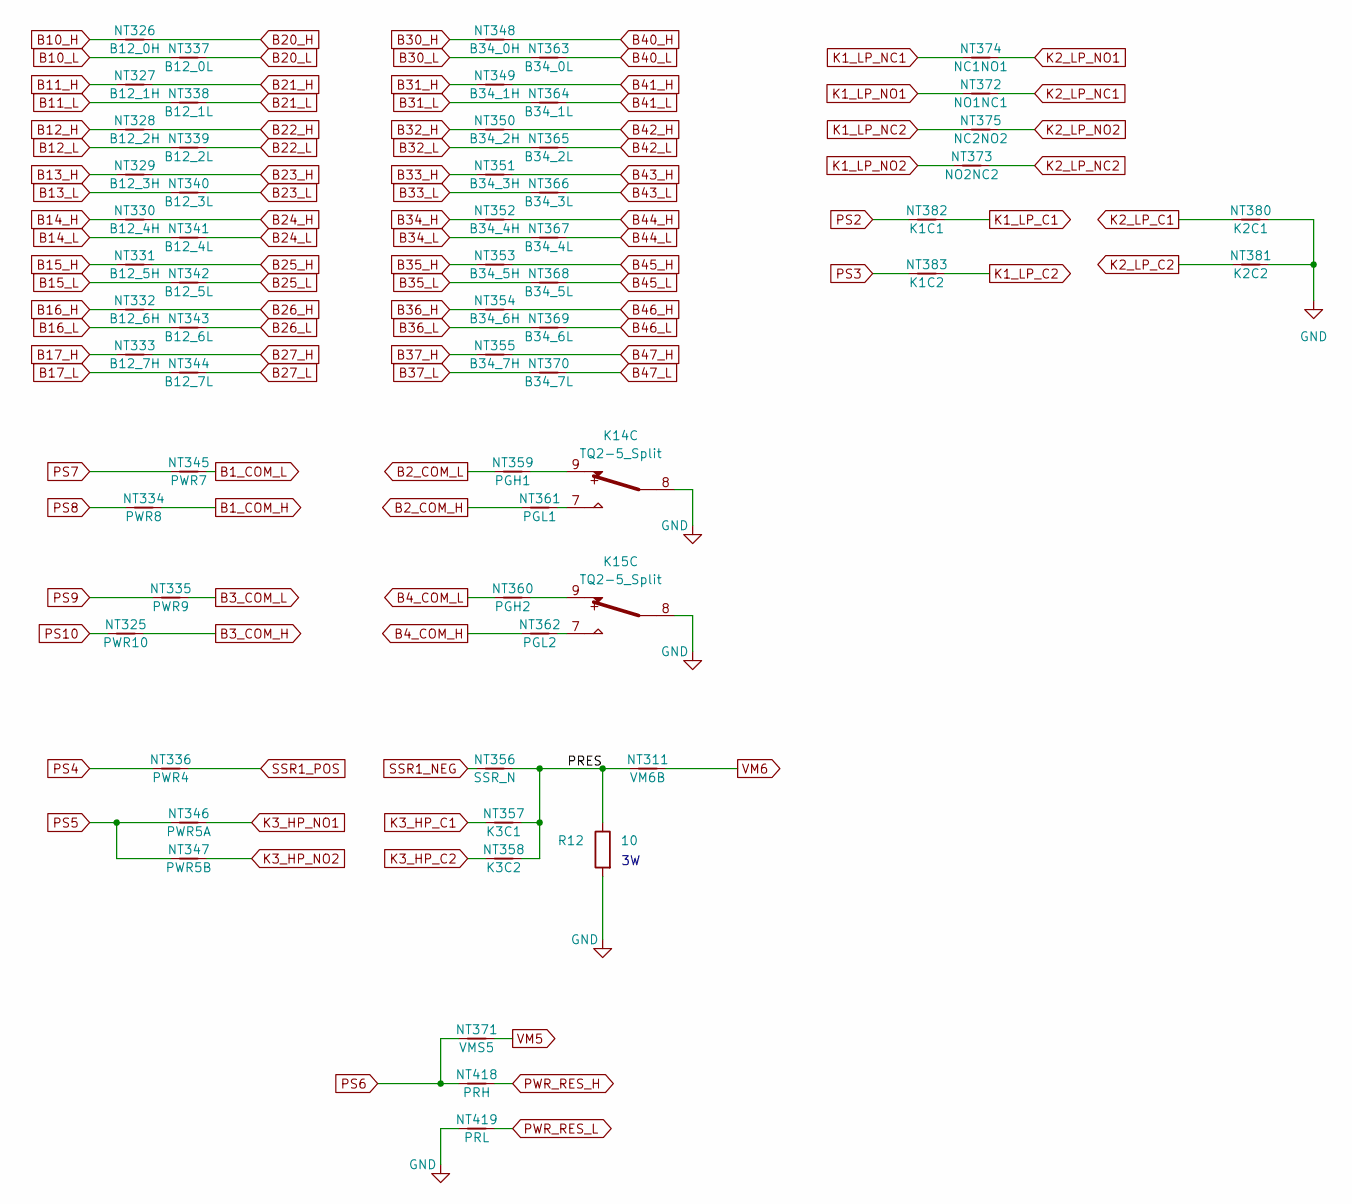
[picture p26: schematic relay_test.kicad_sch]

Parts:
K14, K15: TQ2-5_Split; Relay_DPDT_FRT5
NT311: VM6B; NetTie-2_Front1.0mm
NT325: PWR10; NetTie-2_Front1.0mm
NT326: B12_0H; NetTie-2_Front1.0mm
NT327: B12_1H; NetTie-2_Front1.0mm
NT328: B12_2H; NetTie-2_Front1.0mm
NT329: B12_3H; NetTie-2_Front1.0mm
NT330: B12_4H; NetTie-2_Front1.0mm
NT331: B12_5H; NetTie-2_Front1.0mm
NT332: B12_6H; NetTie-2_Front1.0mm
NT333: B12_7H; NetTie-2_Front1.0mm
NT334: PWR8; NetTie-2_Front1.0mm
NT335: PWR9; NetTie-2_Front1.0mm
NT336: PWR4; NetTie-2_Front1.0mm
NT337: B12_0L; NetTie-2_Front1.0mm
NT338: B12_1L; NetTie-2_Front1.0mm
NT339: B12_2L; NetTie-2_Front1.0mm
NT340: B12_3L; NetTie-2_Front1.0mm
NT341: B12_4L; NetTie-2_Front1.0mm
NT342: B12_5L; NetTie-2_Front1.0mm
NT343: B12_6L; NetTie-2_Front1.0mm
NT344: B12_7L; NetTie-2_Front1.0mm
NT345: PWR7; NetTie-2_Front1.0mm
NT346: PWR5A; NetTie-2_Front1.0mm
NT347: PWR5B; NetTie-2_Front1.0mm
NT348: B34_0H; NetTie-2_Front1.0mm
NT349: B34_1H; NetTie-2_Front1.0mm
NT350: B34_2H; NetTie-2_Front1.0mm
NT351: B34_3H; NetTie-2_Front1.0mm
NT352: B34_4H; NetTie-2_Front1.0mm
NT353: B34_5H; NetTie-2_Front1.0mm
NT354: B34_6H; NetTie-2_Front1.0mm
NT355: B34_7H; NetTie-2_Front1.0mm
NT356: SSR_N; NetTie-2_Front1.0mm
NT357: K3C1; NetTie-2_Front1.0mm
NT358: K3C2; NetTie-2_Front1.0mm
NT359: PGH1; NetTie-2_Front1.0mm
NT360: PGH2; NetTie-2_Front1.0mm
NT361: PGL1; NetTie-2_Front1.0mm
NT362: PGL2; NetTie-2_Front1.0mm
NT363: B34_0L; NetTie-2_Front1.0mm
NT364: B34_1L; NetTie-2_Front1.0mm
NT365: B34_2L; NetTie-2_Front1.0mm
NT366: B34_3L; NetTie-2_Front1.0mm
NT367: B34_4L; NetTie-2_Front1.0mm
NT368: B34_5L; NetTie-2_Front1.0mm
NT369: B34_6L; NetTie-2_Front1.0mm
NT370: B34_7L; NetTie-2_Front1.0mm
NT371: VMS5; NetTie-2_Front1.0mm
NT372: NO1NC1; NetTie-2_Front1.0mm
NT373: NO2NC2; NetTie-2_Front1.0mm
NT374: NC1NO1; NetTie-2_Front1.0mm
NT375: NC2NO2; NetTie-2_Front1.0mm
NT380: K2C1; NetTie-2_Front1.0mm
NT381: K2C2; NetTie-2_Front1.0mm
NT382: K1C1; NetTie-2_Front1.0mm
NT383: K1C2; NetTie-2_Front1.0mm
NT418: PRH; NetTie-2_Front1.0mm
NT419: PRL; NetTie-2_Front1.0mm
R12: 10; R_Axial_DIN0617_L17.0mm_D6.0mm_P25.40mm_Horizontal

Connections:
B1_COM_H: NT334.1
B1_COM_L: NT345.1
B2_COM_H: NT361.2
B2_COM_L: NT359.2
B3_COM_H: NT325.1
B3_COM_L: NT335.1
B4_COM_H: NT362.2
B4_COM_L: NT360.2
B10_H: NT326.1
B10_L: NT337.2
B11_H: NT327.1
B11_L: NT338.2
B12_H: NT328.1
B12_L: NT339.2
B13_H: NT329.1
B13_L: NT340.2
B14_H: NT330.1
B14_L: NT341.2
B15_H: NT331.1
B15_L: NT342.2
B16_H: NT332.1
B16_L: NT343.2
B17_H: NT333.1
B17_L: NT344.2
B20_H: NT326.2
B20_L: NT337.1
B21_H: NT327.2
B21_L: NT338.1
B22_H: NT328.2
B22_L: NT339.1
B23_H: NT329.2
B23_L: NT340.1
B24_H: NT330.2
B24_L: NT341.1
B25_H: NT331.2
B25_L: NT342.1
B26_H: NT332.2
B26_L: NT343.1
B27_H: NT333.2
B27_L: NT344.1
B30_H: NT348.1
B30_L: NT363.2
B31_H: NT349.1
B31_L: NT364.2
B32_H: NT350.1
B32_L: NT365.2
B33_H: NT351.1
B33_L: NT366.2
B34_H: NT352.1
B34_L: NT367.2
B35_H: NT353.1
B35_L: NT368.2
B36_H: NT354.1
B36_L: NT369.2
B37_H: NT355.1
B37_L: NT370.2
B40_H: NT348.2
B40_L: NT363.1
B41_H: NT349.2
B41_L: NT364.1
B42_H: NT350.2
B42_L: NT365.1
B43_H: NT351.2
B43_L: NT366.1
B44_H: NT352.2
B44_L: NT367.1
B45_H: NT353.2
B45_L: NT368.1
B46_H: NT354.2
B46_L: NT369.1
B47_H: NT355.2
B47_L: NT370.1
GND: K14.8, K15.8, NT380.1, NT381.1, NT419.2, R12.2
K1_LP_C1: NT382.2
K1_LP_C2: NT383.2
K1_LP_NC1: NT374.2
K1_LP_NC2: NT375.2
K1_LP_NO1: NT372.2
K1_LP_NO2: NT373.1
K2_LP_C1: NT380.2
K2_LP_C2: NT381.2
K2_LP_NC1: NT372.1
K2_LP_NC2: NT373.2
K2_LP_NO1: NT374.1
K2_LP_NO2: NT375.1
K3_HP_C1: NT357.2
K3_HP_C2: NT358.2
K3_HP_NO1: NT346.1
K3_HP_NO2: NT347.1
unnamed: K14.7, NT361.1
unnamed: K14.9, NT359.1
unnamed: K15.7, NT362.1
unnamed: K15.9, NT360.1
PRES: NT311.1, NT356.1, NT357.1, NT358.1, R12.1
PS2: NT382.1
PS3: NT383.1
PS4: NT336.2
PS5: NT346.2, NT347.2
PS6: NT371.1, NT418.2
PS7: NT345.2
PS8: NT334.2
PS9: NT335.2
PS10: NT325.2
PWR_RES_H: NT418.1
PWR_RES_L: NT419.1
SSR1_NEG: NT356.2
SSR1_POS: NT336.1
VM5: NT371.2
VM6: NT311.2
