dlock8/Selftest_Board/selftest_bd/rswitch.kicad_sch

## KiCad design selftest_bd/rswitch.kicad_sch (2024-11-22)

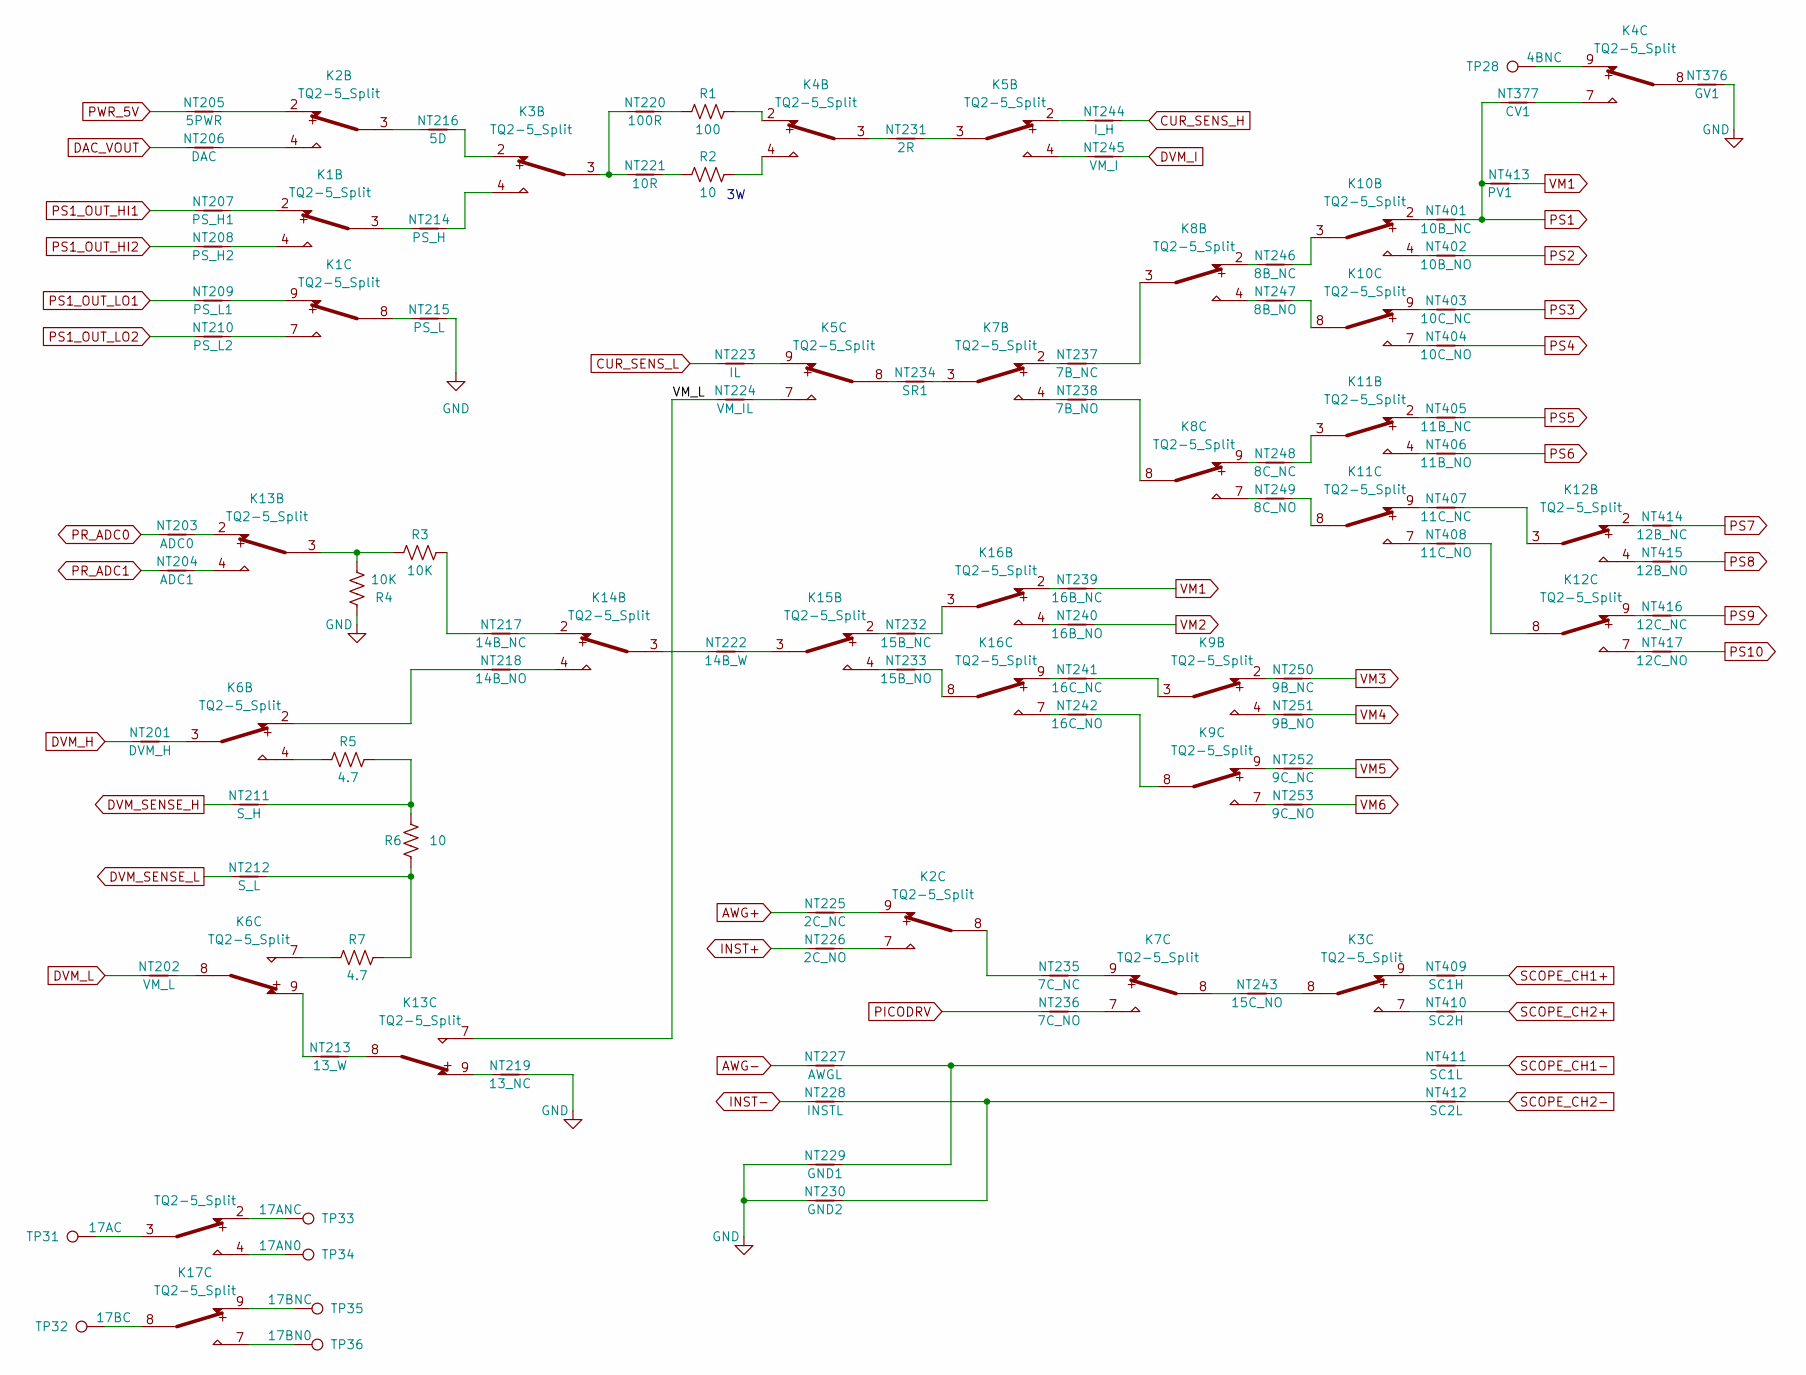
[picture p27: schematic rswitch.kicad_sch]

Parts:
K1, K2, K3, K4, K5, K6, K7, K8, K9, K10, K11, K12, K13, K14, K15, K16, K17: TQ2-5_Split; Relay_DPDT_FRT5
NT201: DVM_H; NetTie-2_Front1.0mm
NT202: VM_L; NetTie-2_Front1.0mm
NT203: ADC0; NetTie-2_Front1.0mm
NT204: ADC1; NetTie-2_Front1.0mm
NT205: 5PWR; NetTie-2_Front1.0mm
NT206: DAC; NetTie-2_Front1.0mm
NT207: PS_H1; NetTie-2_Front1.0mm
NT208: PS_H2; NetTie-2_Front1.0mm
NT209: PS_L1; NetTie-2_Front1.0mm
NT210: PS_L2; NetTie-2_Front1.0mm
NT211: S_H; NetTie-2_Front1.0mm
NT212: S_L; NetTie-2_Front1.0mm
NT213: 13_W; NetTie-2_Front1.0mm
NT214: PS_H; NetTie-2_Front1.0mm
NT215: PS_L; NetTie-2_Front1.0mm
NT216: 5D; NetTie-2_Front1.0mm
NT217: 14B_NC; NetTie-2_Front1.0mm
NT218: 14B_NO; NetTie-2_Front1.0mm
NT219: 13_NC; NetTie-2_Front1.0mm
NT220: 100R; NetTie-2_Front1.0mm
NT221: 10R; NetTie-2_Front1.0mm
NT222: 14B_W; NetTie-2_Front1.0mm
NT223: IL; NetTie-2_Front1.0mm
NT224: VM_IL; NetTie-2_Front1.0mm
NT225: 2C_NC; NetTie-2_Front1.0mm
NT226: 2C_NO; NetTie-2_Front1.0mm
NT227: AWGL; NetTie-2_Front1.0mm
NT228: INSTL; NetTie-2_Front1.0mm
NT229: GND1; NetTie-2_Front1.0mm
NT230: GND2; NetTie-2_Front1.0mm
NT231: 2R; NetTie-2_Front1.0mm
NT232: 15B_NC; NetTie-2_Front1.0mm
NT233: 15B_NO; NetTie-2_Front1.0mm
NT234: SR1; NetTie-2_Front1.0mm
NT235: 7C_NC; NetTie-2_Front1.0mm
NT236: 7C_NO; NetTie-2_Front1.0mm
NT237: 7B_NC; NetTie-2_Front1.0mm
NT238: 7B_NO; NetTie-2_Front1.0mm
NT239: 16B_NC; NetTie-2_Front1.0mm
NT240: 16B_NO; NetTie-2_Front1.0mm
NT241: 16C_NC; NetTie-2_Front1.0mm
NT242: 16C_NO; NetTie-2_Front1.0mm
NT243: 15C_NO; NetTie-2_Front1.0mm
NT244: I_H; NetTie-2_Front1.0mm
NT245: VM_I; NetTie-2_Front1.0mm
NT246: 8B_NC; NetTie-2_Front1.0mm
NT247: 8B_NO; NetTie-2_Front1.0mm
NT248: 8C_NC; NetTie-2_Front1.0mm
NT249: 8C_NO; NetTie-2_Front1.0mm
NT250: 9B_NC; NetTie-2_Front1.0mm
NT251: 9B_NO; NetTie-2_Front1.0mm
NT252: 9C_NC; NetTie-2_Front1.0mm
NT253: 9C_NO; NetTie-2_Front1.0mm
NT376: GV1; NetTie-2_Front1.0mm
NT377: CV1; NetTie-2_Front1.0mm
NT401: 10B_NC; NetTie-2_Front1.0mm
NT402: 10B_NO; NetTie-2_Front1.0mm
NT403: 10C_NC; NetTie-2_Front1.0mm
NT404: 10C_NO; NetTie-2_Front1.0mm
NT405: 11B_NC; NetTie-2_Front1.0mm
NT406: 11B_NO; NetTie-2_Front1.0mm
NT407: 11C_NC; NetTie-2_Front1.0mm
NT408: 11C_NO; NetTie-2_Front1.0mm
NT409: SC1H; NetTie-2_Front1.0mm
NT410: SC2H; NetTie-2_Front1.0mm
NT411: SC1L; NetTie-2_Front1.0mm
NT412: SC2L; NetTie-2_Front1.0mm
NT413: PV1; NetTie-2_Front1.0mm
NT414: 12B_NC; NetTie-2_Front1.0mm
NT415: 12B_NO; NetTie-2_Front1.0mm
NT416: 12C_NC; NetTie-2_Front1.0mm
NT417: 12C_NO; NetTie-2_Front1.0mm
R1: 100; R_Axial_DIN0207_L6.3mm_D2.5mm_P10.16mm_Horizontal
R2: 10; R_Axial_DIN0617_L17.0mm_D6.0mm_P25.40mm_Horizontal
R3, R4: 10K; R_Axial_DIN0207_L6.3mm_D2.5mm_P10.16mm_Horizontal
R5, R7: 4.7; R_Axial_DIN0207_L6.3mm_D2.5mm_P10.16mm_Horizontal
R6: 10; R_Axial_DIN0207_L6.3mm_D2.5mm_P10.16mm_Horizontal
TP28: 4BNC; TestPoint_THTPad_D1.5mm_Drill0.7mm
TP31: 17AC; TestPoint_THTPad_D1.5mm_Drill0.7mm
TP32: 17BC; TestPoint_THTPad_D1.5mm_Drill0.7mm
TP33: 17ANC; TestPoint_THTPad_D1.5mm_Drill0.7mm
TP34: 17AN0; TestPoint_THTPad_D1.5mm_Drill0.7mm
TP35: 17BNC; TestPoint_THTPad_D1.5mm_Drill0.7mm
TP36: 17BN0; TestPoint_THTPad_D1.5mm_Drill0.7mm

Connections:
AWG+: NT225.1
AWG-: NT227.1
CUR_SENS_H: NT244.2
CUR_SENS_L: NT223.1
DAC_VOUT: NT206.1
DVM_H: NT201.1
DVM_I: NT245.2
DVM_L: NT202.1
DVM_SENSE_H: NT211.1
DVM_SENSE_L: NT212.1
GND: NT215.2, NT219.2, NT229.1, NT230.1, NT376.2, R4.1
INST+: NT226.1
INST-: NT228.1
unnamed: K1.2, NT207.2
unnamed: K1.3, NT214.1
unnamed: K1.4, NT208.2
unnamed: K1.7, NT210.2
unnamed: K1.8, NT215.1
unnamed: K1.9, NT209.2
unnamed: K2.2, NT205.2
unnamed: K2.3, NT216.1
unnamed: K2.4, NT206.2
unnamed: K2.7, NT226.2
unnamed: K2.8, NT235.1
unnamed: K2.9, NT225.2
unnamed: K3.2, NT216.2
unnamed: K3.3, NT220.1, NT221.1
unnamed: K3.4, NT214.2
unnamed: K3.7, NT410.1
unnamed: K3.8, NT243.2
unnamed: K3.9, NT409.1
unnamed: K4.2, R1.1
unnamed: K4.3, NT231.1
unnamed: K4.4, R2.1
unnamed: K4.7, NT377.2
unnamed: K4.8, NT376.1
unnamed: K4.9, TP28.1
unnamed: K5.2, NT244.1
unnamed: K5.3, NT231.2
unnamed: K5.4, NT245.1
unnamed: K5.7, NT224.2
unnamed: K5.8, NT234.1
unnamed: K5.9, NT223.2
unnamed: K6.2, NT218.1
unnamed: K6.3, NT201.2
unnamed: K6.4, R5.2
unnamed: K6.7, R7.2
unnamed: K6.8, NT202.2
unnamed: K6.9, NT213.1
unnamed: K7.2, NT237.1
unnamed: K7.3, NT234.2
unnamed: K7.4, NT238.1
unnamed: K7.7, NT236.2
unnamed: K7.8, NT243.1
unnamed: K7.9, NT235.2
unnamed: K8.2, NT246.1
unnamed: K8.3, NT237.2
unnamed: K8.4, NT247.1
unnamed: K8.7, NT249.1
unnamed: K8.8, NT238.2
unnamed: K8.9, NT248.1
unnamed: K9.2, NT250.1
unnamed: K9.3, NT241.2
unnamed: K9.4, NT251.1
unnamed: K9.7, NT253.1
unnamed: K9.8, NT242.2
unnamed: K9.9, NT252.1
unnamed: K10.2, NT401.1
unnamed: K10.3, NT246.2
unnamed: K10.4, NT402.1
unnamed: K10.7, NT404.1
unnamed: K10.8, NT247.2
unnamed: K10.9, NT403.1
unnamed: K11.2, NT405.1
unnamed: K11.3, NT248.2
unnamed: K11.4, NT406.1
unnamed: K11.7, NT408.1
unnamed: K11.8, NT249.2
unnamed: K11.9, NT407.1
unnamed: K12.2, NT414.1
unnamed: K12.3, NT407.2
unnamed: K12.4, NT415.1
unnamed: K12.7, NT417.1
unnamed: K12.8, NT408.2
unnamed: K12.9, NT416.1
unnamed: K13.2, NT203.2
unnamed: K13.3, R3.2, R4.2
unnamed: K13.4, NT204.2
unnamed: K13.8, NT213.2
unnamed: K13.9, NT219.1
unnamed: K14.2, NT217.2
unnamed: K14.3, NT222.1
unnamed: K14.4, NT218.2
unnamed: K15.2, NT232.1
unnamed: K15.3, NT222.2
unnamed: K15.4, NT233.1
unnamed: K16.2, NT239.1
unnamed: K16.3, NT232.2
unnamed: K16.4, NT240.1
unnamed: K16.7, NT242.1
unnamed: K16.8, NT233.2
unnamed: K16.9, NT241.1
unnamed: K17.2, TP33.1
unnamed: K17.3, TP31.1
unnamed: K17.4, TP34.1
unnamed: K17.7, TP36.1
unnamed: K17.8, TP32.1
unnamed: K17.9, TP35.1
unnamed: NT211.2, R5.1, R6.2
unnamed: NT212.2, R6.1, R7.1
unnamed: NT217.1, R3.1
unnamed: NT220.2, R1.2
unnamed: NT221.2, R2.2
unnamed: NT227.2, NT229.2, NT411.1
unnamed: NT228.2, NT230.2, NT412.1
PICODRV: NT236.1
PR_ADC0: NT203.1
PR_ADC1: NT204.1
PS1: NT377.1, NT401.2, NT413.1
PS1_OUT_HI1: NT207.1
PS1_OUT_HI2: NT208.1
PS1_OUT_LO1: NT209.1
PS1_OUT_LO2: NT210.1
PS2: NT402.2
PS3: NT403.2
PS4: NT404.2
PS5: NT405.2
PS6: NT406.2
PS7: NT414.2
PS8: NT415.2
PS9: NT416.2
PS10: NT417.2
PWR_5V: NT205.1
SCOPE_CH1+: NT409.2
SCOPE_CH1-: NT411.2
SCOPE_CH2+: NT410.2
SCOPE_CH2-: NT412.2
VM1: NT239.2, NT413.2
VM2: NT240.2
VM3: NT250.2
VM4: NT251.2
VM5: NT252.2
VM6: NT253.2
VM_L: K13.7, NT224.1
