dlock8/Selftest_Board/selftest_bd/test_connector.kicad_sch

## KiCad design selftest_bd/test_connector.kicad_sch (2024-11-22)

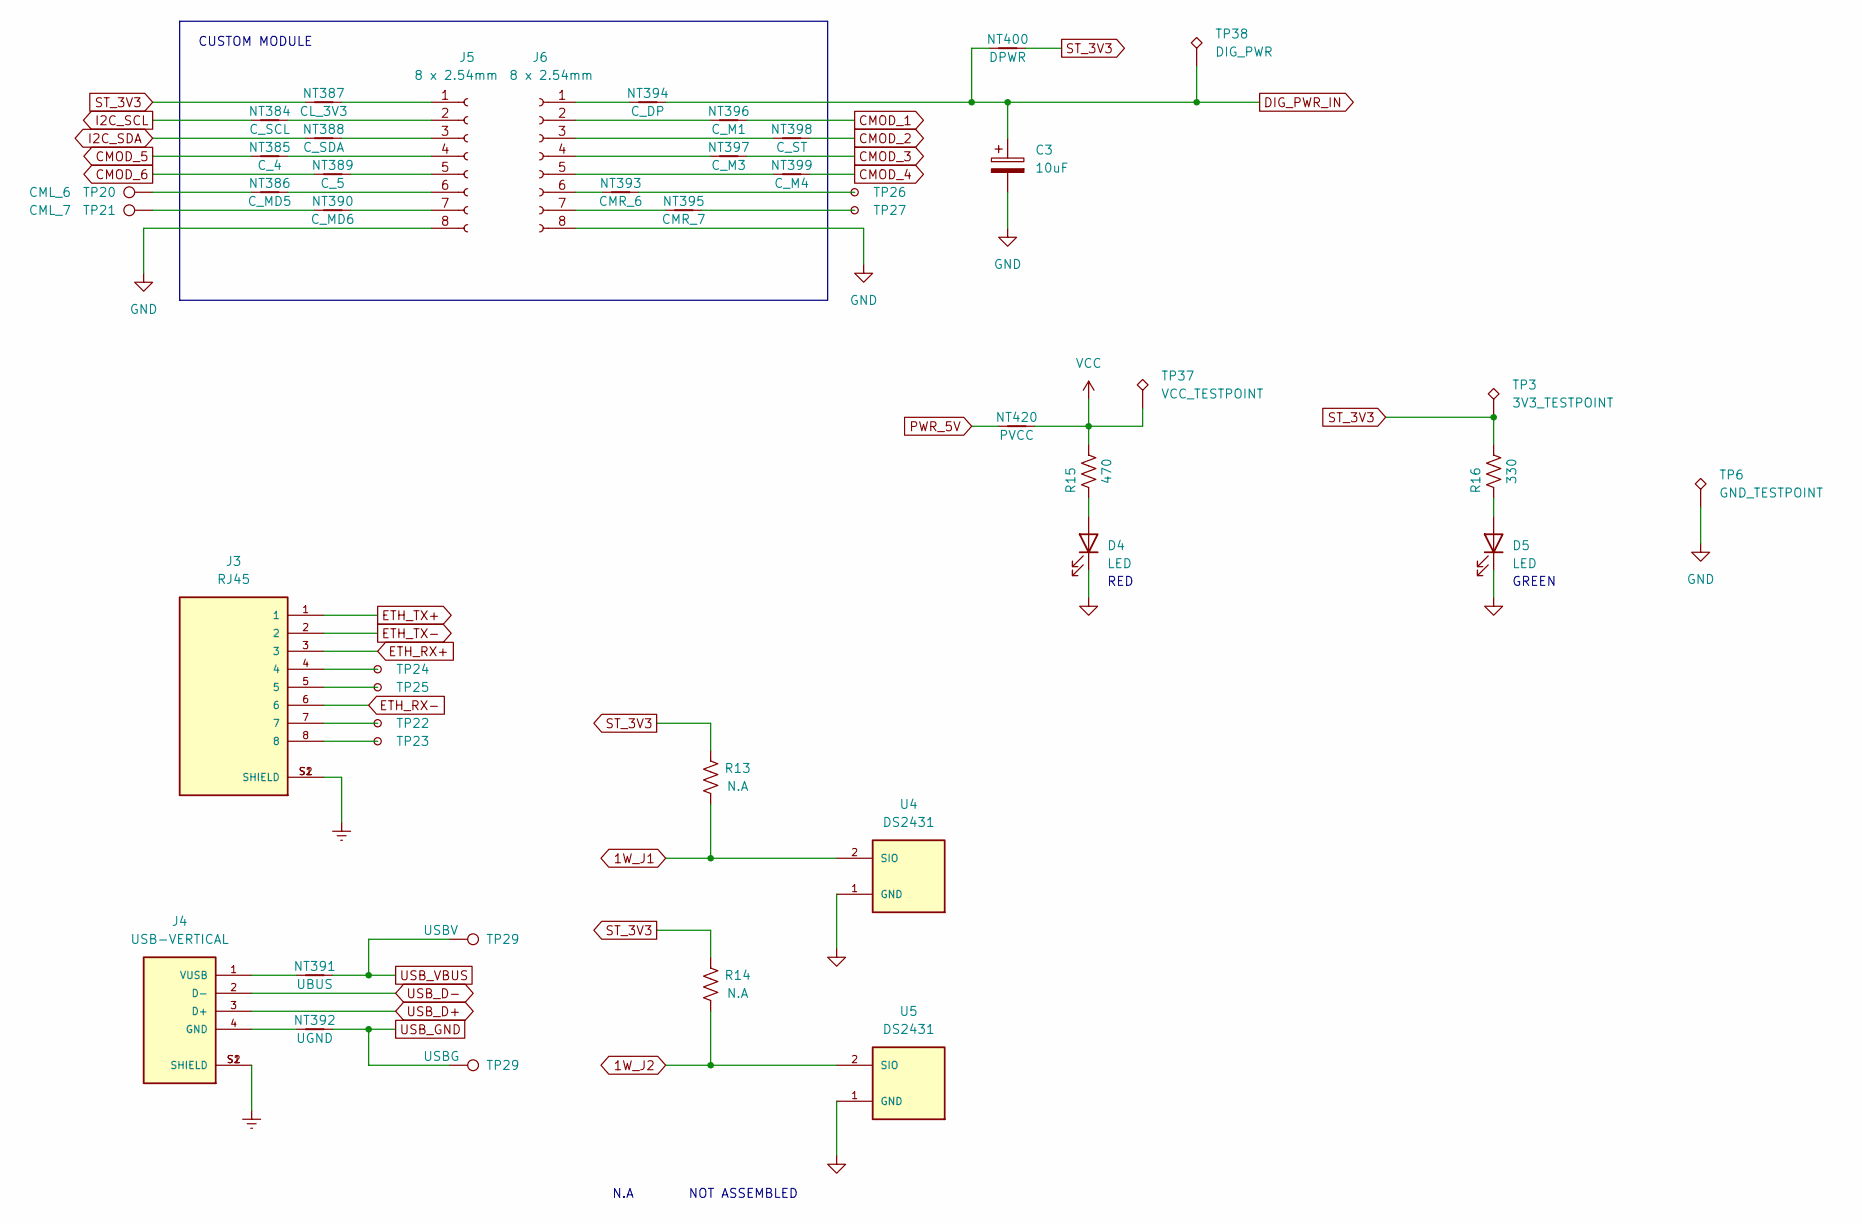
[picture p28: schematic test_connector.kicad_sch]

Parts:
C3: 10uF; CP_Radial_Tantal_D4.5mm_P2.50mm
D4, D5: LED; LED_D3.0mm
J3: RJ45; CUI_CRJ028-1H-TH; PARTREV 1.0
J4: USB-VERTICAL; ONSHORE_USB-A1VSB6; PARTREV D
J5, J6: 8 x 2.54mm; PinSocket_1x08_P2.54mm_Vertical
NT384: C_SCL; NetTie-2_Front1.0mm
NT385: C_4; NetTie-2_Front1.0mm
NT386: C_MD5; NetTie-2_Front1.0mm
NT387: CL_3V3; NetTie-2_Front1.0mm
NT388: C_SDA; NetTie-2_Front1.0mm
NT389: C_5; NetTie-2_Front1.0mm
NT390: C_MD6; NetTie-2_Front1.0mm
NT391: UBUS; NetTie-2_Front1.0mm
NT392: UGND; NetTie-2_Front1.0mm
NT393: CMR_6; NetTie-2_Front1.0mm
NT394: C_DP; NetTie-2_Front1.0mm
NT395: CMR_7; NetTie-2_Front1.0mm
NT396: C_M1; NetTie-2_Front1.0mm
NT397: C_M3; NetTie-2_Front1.0mm
NT398: C_ST; NetTie-2_Front1.0mm
NT399: C_M4; NetTie-2_Front1.0mm
NT400: DPWR; NetTie-2_Front1.0mm
NT420: PVCC; NetTie-2_Front1.0mm
R13, R14: N.A; R_Axial_DIN0207_L6.3mm_D2.5mm_P10.16mm_Horizontal
R15: 470; R_Axial_DIN0207_L6.3mm_D2.5mm_P10.16mm_Horizontal
R16: 330; R_Axial_DIN0207_L6.3mm_D2.5mm_P10.16mm_Horizontal
TP3: 3V3_TESTPOINT; TestPoint_Loop_D2.54mm_Drill1.5mm_Beaded
TP6: GND_TESTPOINT; TestPoint_Loop_D2.54mm_Drill1.5mm_Beaded
TP20: CML_6; TestPoint_THTPad_D1.5mm_Drill0.7mm
TP21: CML_7; TestPoint_THTPad_D1.5mm_Drill0.7mm
TP22, TP23, TP24, TP25, TP26, TP27: TestPoint_Small; TestPoint_THTPad_D1.5mm_Drill0.7mm
TP29: USBG; TestPoint_THTPad_D1.5mm_Drill0.7mm
TP37: VCC_TESTPOINT; TestPoint_Loop_D2.54mm_Drill1.5mm_Beaded
TP38: DIG_PWR; TestPoint_Loop_D2.54mm_Drill1.5mm_Beaded
U4, U5: DS2431; TO-92_HandSolder

Connections:
1W_J1: R13.1, U4.2 (SIO)
1W_J2: R14.1, U5.2 (SIO)
CMOD_1: NT396.2
CMOD_2: NT398.2
CMOD_3: NT397.2
CMOD_4: NT399.2
CMOD_5: NT385.1
CMOD_6: NT389.1
DIG_PWR_IN: C3.1, NT394.2, NT400.1, TP38.1
ETH_RX+: J3.3
ETH_RX-: J3.6
ETH_TX+: J3.1
ETH_TX-: J3.2
Earth: J3.S1 (SHIELD), J3.S2 (SHIELD), J4.S1 (SHIELD), J4.S2 (SHIELD)
GND: C3.2, D4.1 (K), D5.1 (K), J5.8, J6.8, TP6.1, U4.1 (GND), U5.1 (GND)
I2C_SCL: NT384.1
I2C_SDA: NT388.1
unnamed: D4.2 (A), R15.1
unnamed: D5.2 (A), R16.1
unnamed: J3.4, TP24.1
unnamed: J3.5, TP25.1
unnamed: J3.7, TP22.1
unnamed: J3.8, TP23.1
unnamed: J4.1 (VUSB), NT391.1
unnamed: J4.4 (GND), NT392.1
unnamed: J5.1, NT387.2
unnamed: J5.2, NT384.2
unnamed: J5.3, NT388.2
unnamed: J5.4, NT385.2
unnamed: J5.5, NT389.2
unnamed: J5.6, NT386.1
unnamed: J5.7, NT390.1
unnamed: J6.1, NT394.1
unnamed: J6.2, NT396.1
unnamed: J6.3, NT398.1
unnamed: J6.4, NT397.1
unnamed: J6.5, NT399.1
unnamed: J6.6, NT393.1
unnamed: J6.7, NT395.1
unnamed: NT386.2, TP20.1
unnamed: NT390.2, TP21.1
unnamed: NT393.2, TP26.1
unnamed: NT395.2, TP27.1
PWR_5V: NT420.1
ST_3V3: NT387.1, NT400.2, R13.2, R14.2, R16.2, TP3.1
USB_D+: J4.3 (D+)
USB_D-: J4.2 (D-)
USB_GND: NT392.2, TP29.1
USB_VBUS: NT391.2, TP29.1
VCC: NT420.2, R15.2, TP37.1

Notes on the sheet:
N.A NOT ASSEMBLED
GREEN
RED
CUSTOM MODULE
